Robomarchello/PixelSketch/src/states/state.py

class State:
    def __init__(self, state_machine):
        self.state_machine = state_machine

    def logic(self):
        pass

    def on_enter(self):
        pass
    
    def on_exit(self):
        pass
    
