Robomarchello/PixelSketch/src/config.py

# --- Screen configuration
SCREEN_SIZE = SCREEN_W, SCREEN_H = 480, 320
# display pins
LCD_DC = const(3)
LCD_RST = const(4)
LCD_CS = const(9)
LCD_CLK = const(6)
LCD_MOSI = const(7)
LCD_LED = const(2)

BATTERY_READING_PIN = const(28)

# screen spi (24 MHz max speed on pico)
BAUD_RATE = 24_000_000

ENCODER_R_CLK, ENCODER_R_DT, ENCODER_R_SW = 12, 11, 13
ENCODER_L_CLK, ENCODER_L_DT, ENCODER_L_SW = 20, 19, 18

MOTION_SCL = const(27)
MOTION_SDA = const(26)

GYRO_POLL_MS = 150
SHAKE_THRESHOLD = 10
SHAKE_THRESHOLD *= SHAKE_THRESHOLD

BRUSH_RADIUS = 3
BG_COLOR = 'WHITE'

CHUNK_SIZE = 512
